leonardogargani/jell-e/stl/solidworks/Assieme_Completo - Cover_Upper Closure-1.STL

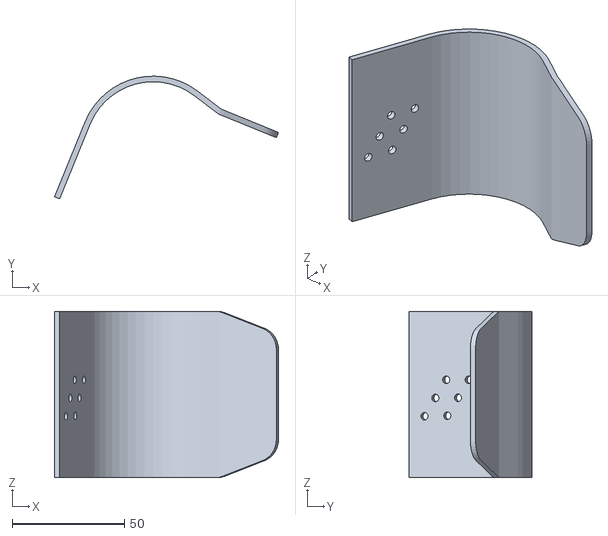
[picture p16: CAD file, 2022-06-20]
stl/solidworks/Assieme_Completo - Cover_Upper Closure-1.STL
99.7 x 54.6 x 74.0
