leonardogargani/jell-e/models/solidworks/Cover_002 - Longer of 2.5.SLDPRT

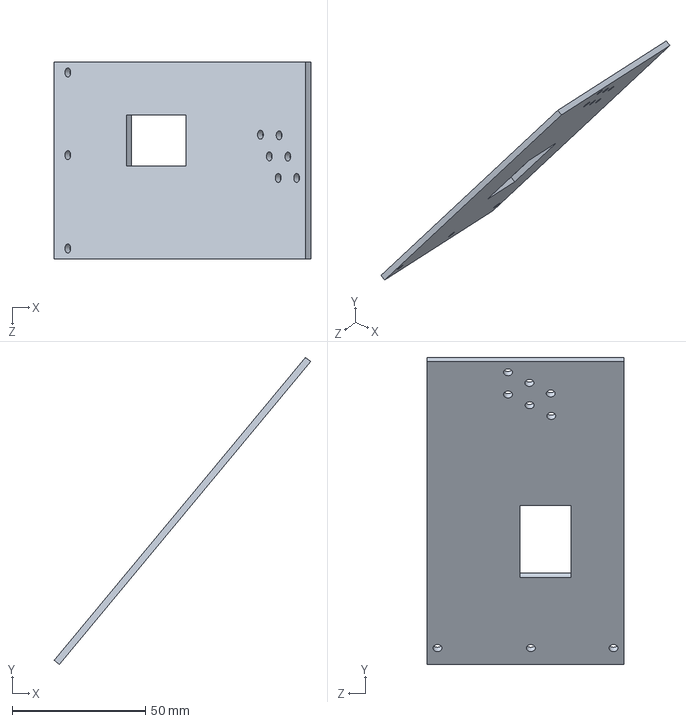
[picture p17: CAD file, 2022-06-20]
models/solidworks/Cover_002 - Longer of 2.5.SLDPRT
96.2 x 115.1 x 74.0 mm
