leonardogargani/jell-e/stl/openscad/logo_plate.stl

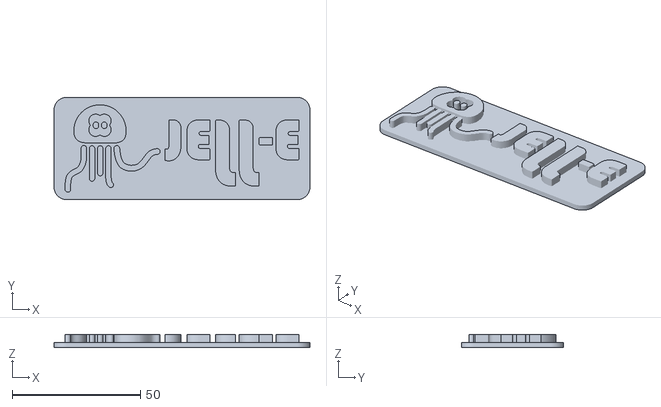
[picture p18: CAD file, 2022-06-20]
stl/openscad/logo_plate.stl
100.0 x 40.0 x 4.99
