leonardogargani/jell-e/stl/solidworks/Assieme_Completo - Cover_Battery and Switch-1.STL

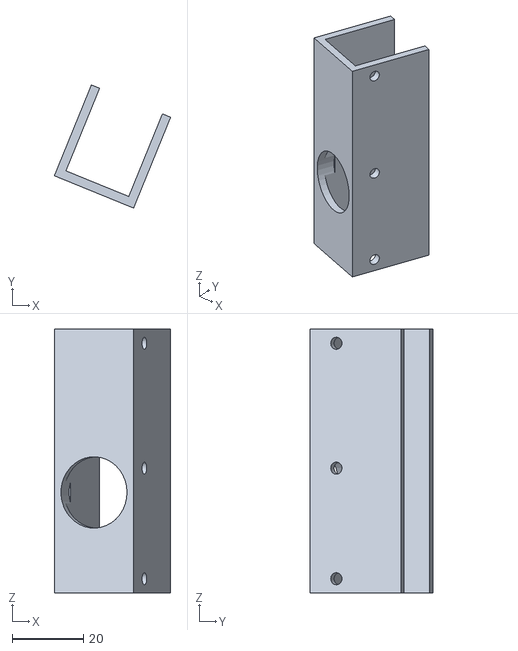
[picture p19: CAD file, 2022-06-20]
stl/solidworks/Assieme_Completo - Cover_Battery and Switch-1.STL
32.6 x 34.5 x 74.0
