leonardogargani/jell-e/models/solidworks/Cover_Upper Closure.SLDPRT

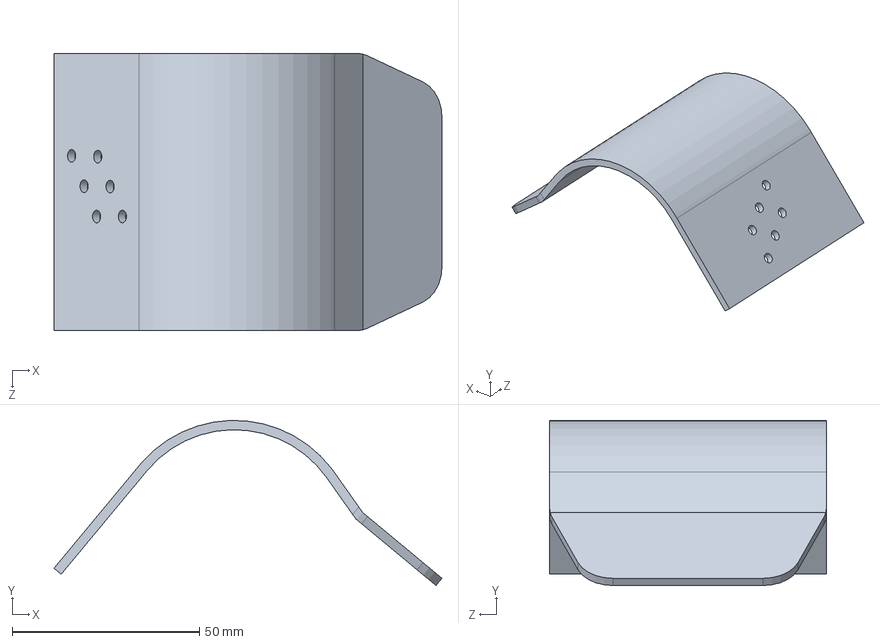
[picture p20: CAD file, 2022-06-20]
models/solidworks/Cover_Upper Closure.SLDPRT
103.7 x 44.1 x 74.0 mm
