leonardogargani/jell-e/stl/openscad/spring.stl

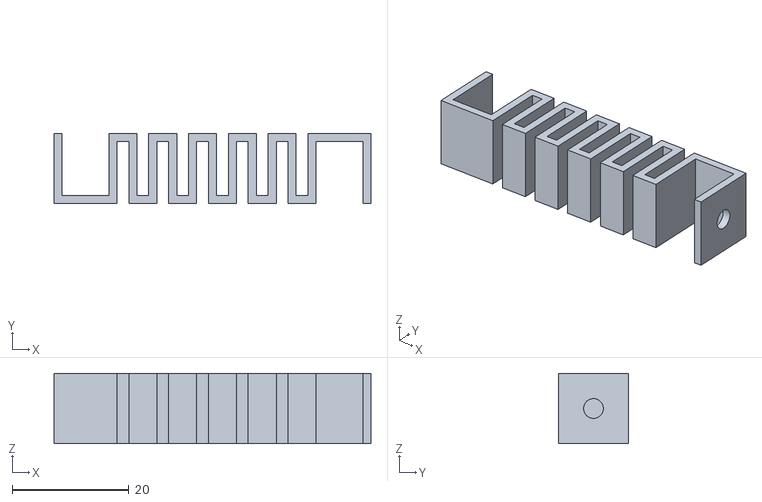
[picture p21: CAD file, 2022-06-20]
stl/openscad/spring.stl
54.2 x 12.0 x 12.0
