leonardogargani/jell-e/stl/solidworks/Assieme_Completo - ServoMotor_Body-2.STL

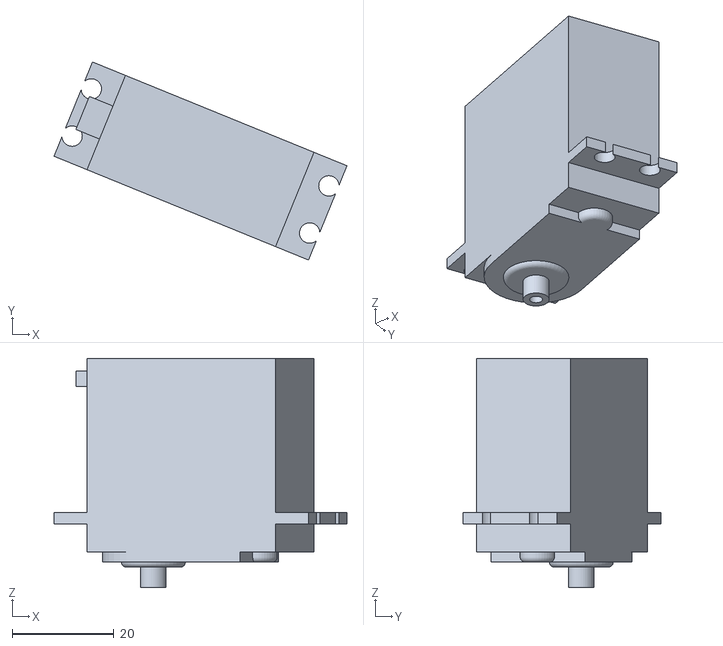
[picture p22: CAD file, 2022-06-20]
stl/solidworks/Assieme_Completo - ServoMotor_Body-2.STL
57.6 x 38.9 x 45.0
