leonardogargani/jell-e/models/solidworks/Internal_Box_001.SLDPRT

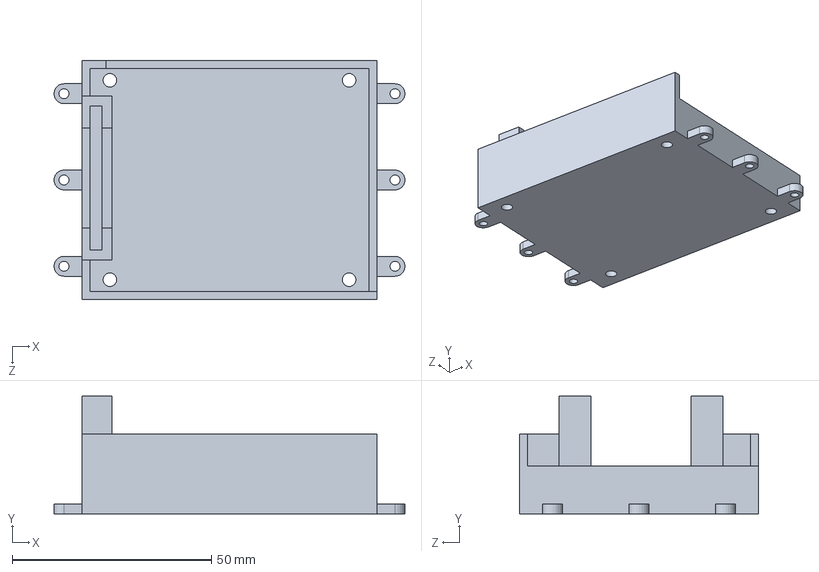
[picture p23: CAD file, 2022-06-20]
models/solidworks/Internal_Box_001.SLDPRT
88.0 x 29.5 x 60.0 mm
