leonardogargani/jell-e/stl/openscad/joint.stl

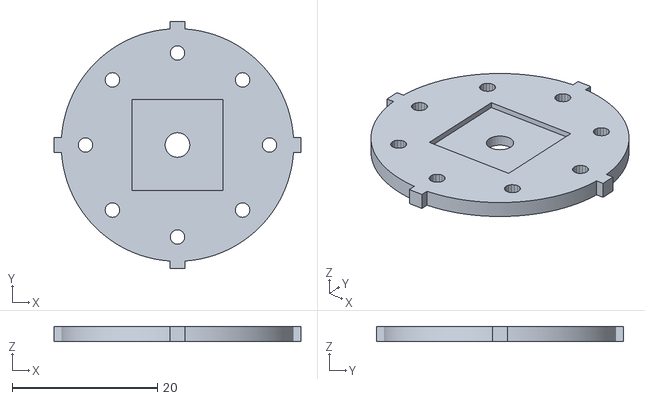
[picture p24: CAD file, 2022-06-20]
stl/openscad/joint.stl
34.0 x 34.0 x 2.00
