leonardogargani/jell-e/stl/solidworks/Assieme_Completo - ServoMotors_Adapter Wing-1.STL

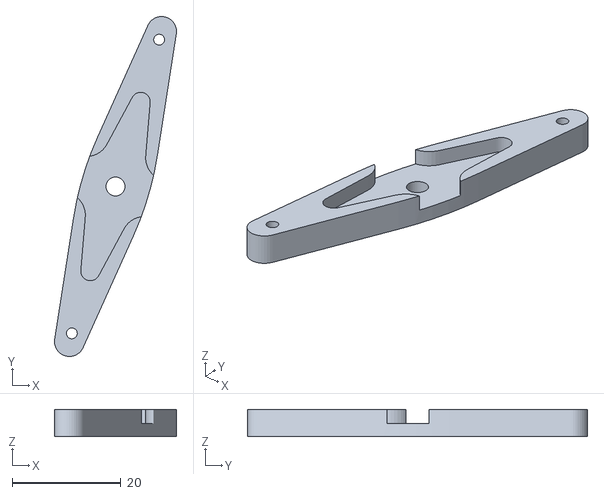
[picture p25: CAD file, 2022-06-20]
stl/solidworks/Assieme_Completo - ServoMotors_Adapter Wing-1.STL
22.4 x 62.5 x 5.00
