leonardogargani/jell-e/models/solidworks/Base_Shoulder Adapter.SLDPRT

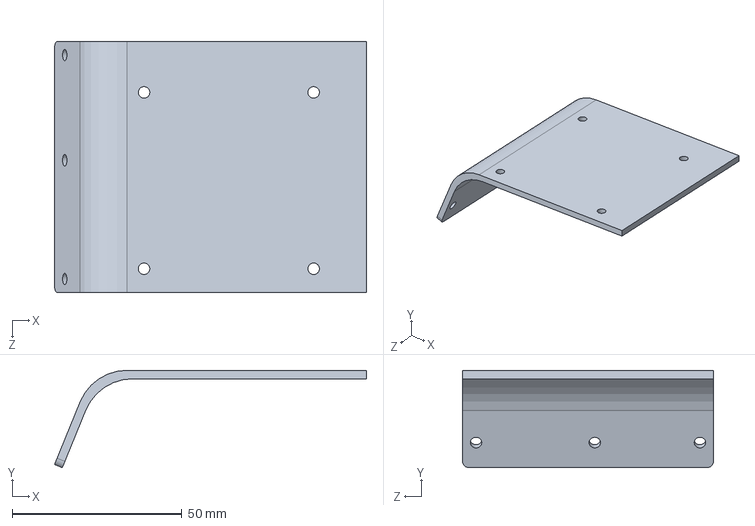
[picture p26: CAD file, 2022-06-20]
models/solidworks/Base_Shoulder Adapter.SLDPRT
92.0 x 28.7 x 74.0 mm
