leonardogargani/jell-e/stl/solidworks/Assieme_Completo - Extra Support-1.STL

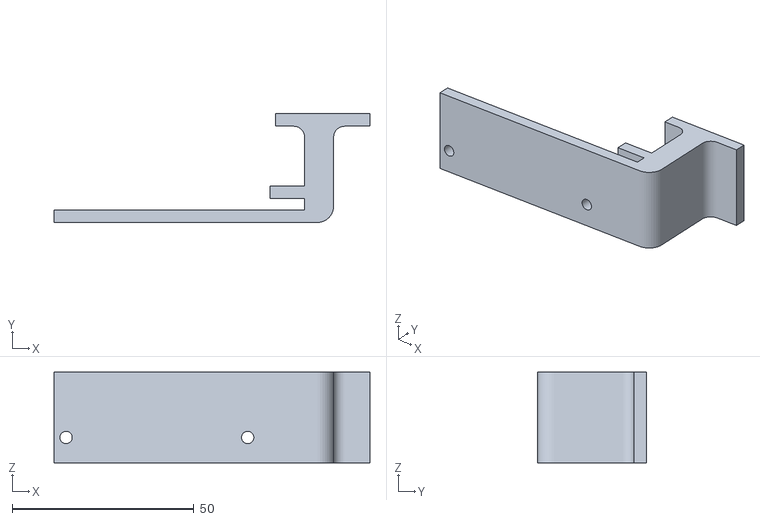
[picture p27: CAD file, 2022-06-20]
stl/solidworks/Assieme_Completo - Extra Support-1.STL
87.0 x 30.0 x 25.0
