leonardogargani/jell-e/models/solidworks/External_Battery.SLDPRT

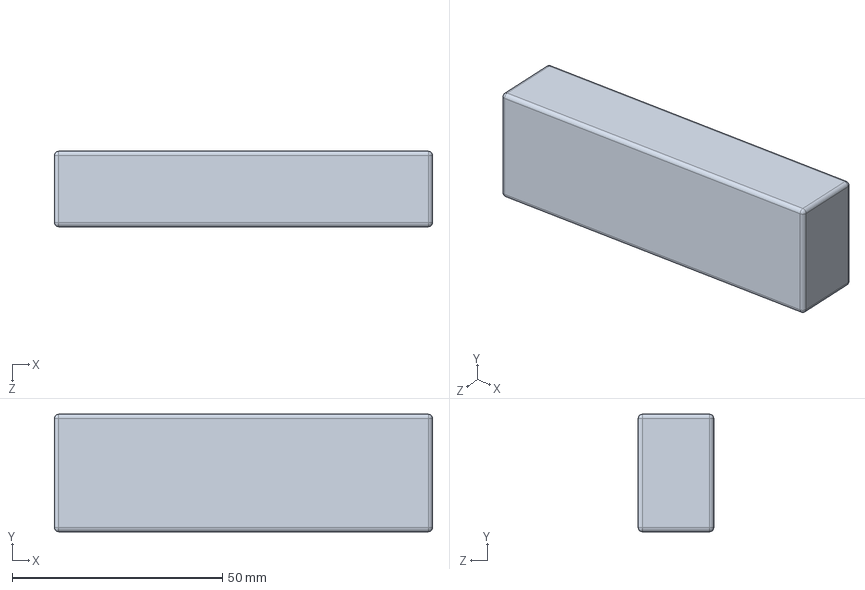
[picture p28: CAD file, 2022-06-20]
models/solidworks/External_Battery.SLDPRT
90.0 x 28.0 x 18.0 mm
