leonardogargani/jell-e/stl/solidworks/Assieme_Completo - External_Battery-1.STL

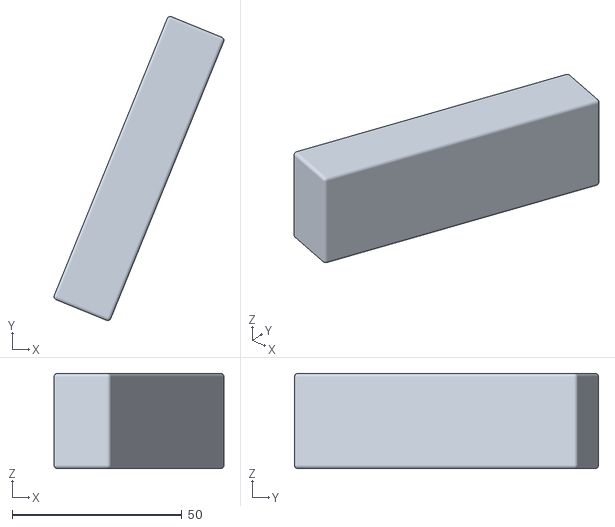
[picture p29: CAD file, 2022-06-20]
stl/solidworks/Assieme_Completo - External_Battery-1.STL
50.0 x 89.5 x 28.0
