leonardogargani/jell-e/stl/solidworks/Assieme_Completo - ServoMotors_AdapterFront-1.STL

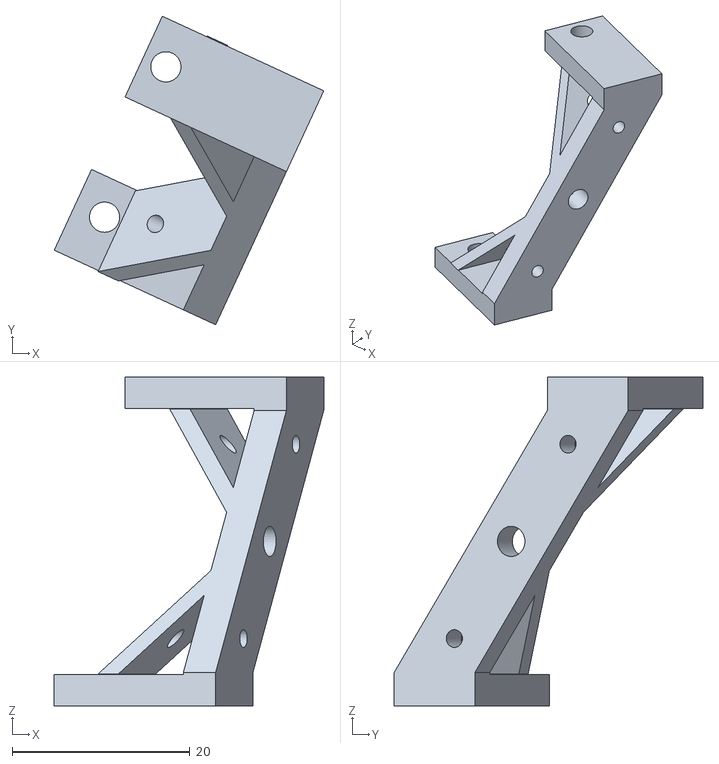
[picture p30: CAD file, 2022-06-20]
stl/solidworks/Assieme_Completo - ServoMotors_AdapterFront-1.STL
30.3 x 34.7 x 37.0
