leonardogargani/jell-e/stl/solidworks/Assieme_Completo - ServoMotors_Adapter Wing-2.STL

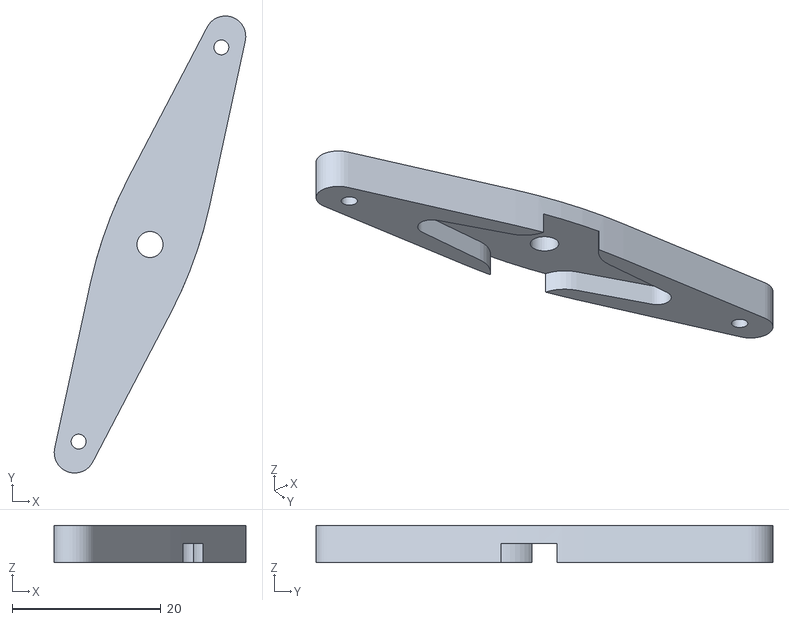
[picture p31: CAD file, 2022-06-20]
stl/solidworks/Assieme_Completo - ServoMotors_Adapter Wing-2.STL
25.8 x 61.4 x 5.00
