leonardogargani/jell-e/models/openscad/logo_plate.scad

include <lib/logo.scad>


logo_plate();
