leonardogargani/jell-e/models/openscad/plate_stand.scad

include <lib/logo.scad>


// uncomment the following line to visualize the plate on its stand
//logo_plate_oblique(difference_mode=false);
plate_stand();
