leonardogargani/jell-e/models/openscad/round_washer.scad

include <lib/tentacle.scad>


round_washer(radius=6, thickness=2);
