leonardogargani/jell-e/models/openscad/tip.scad

include <lib/tentacle.scad>


tip();
