leonardogargani/jell-e/esp32/Include/Devices.h

#ifndef DEVICES_H
#define DEVICES_H

// Sensors
#include "Sensors/Microphone.h"
#include "Sensors/Button.h"
#include "Sensors/UltrasonicSensor.h"

// Actuators
#include "Actuators/LEDStrip.h"
#include "Actuators/Tentacle.h"

#endif
